brad-za/chastity/pictures/choc/v1/left-front.png

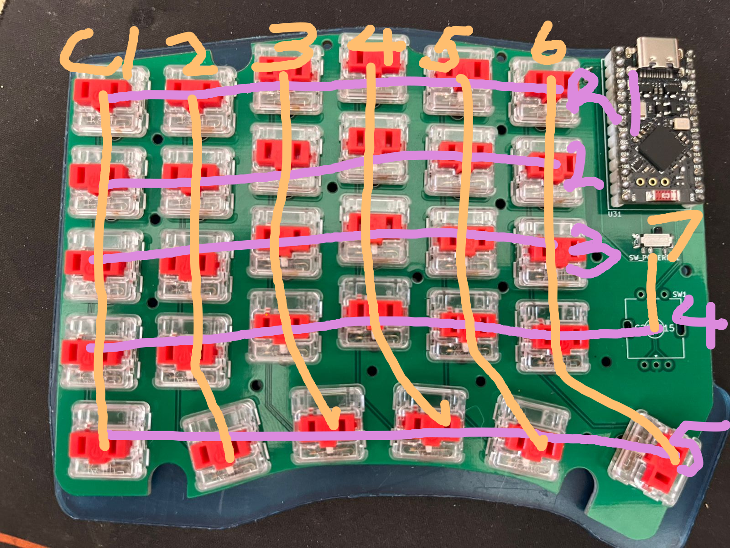
pictures/choc/v1/left-front.png
