brad-za/chastity/kicad/mx/V3/V3 - split/left/chastity.kicad_sch

## KiCad design kicad/mx/V3/V3 - split/left/chastity.kicad_sch (2025-07-24)

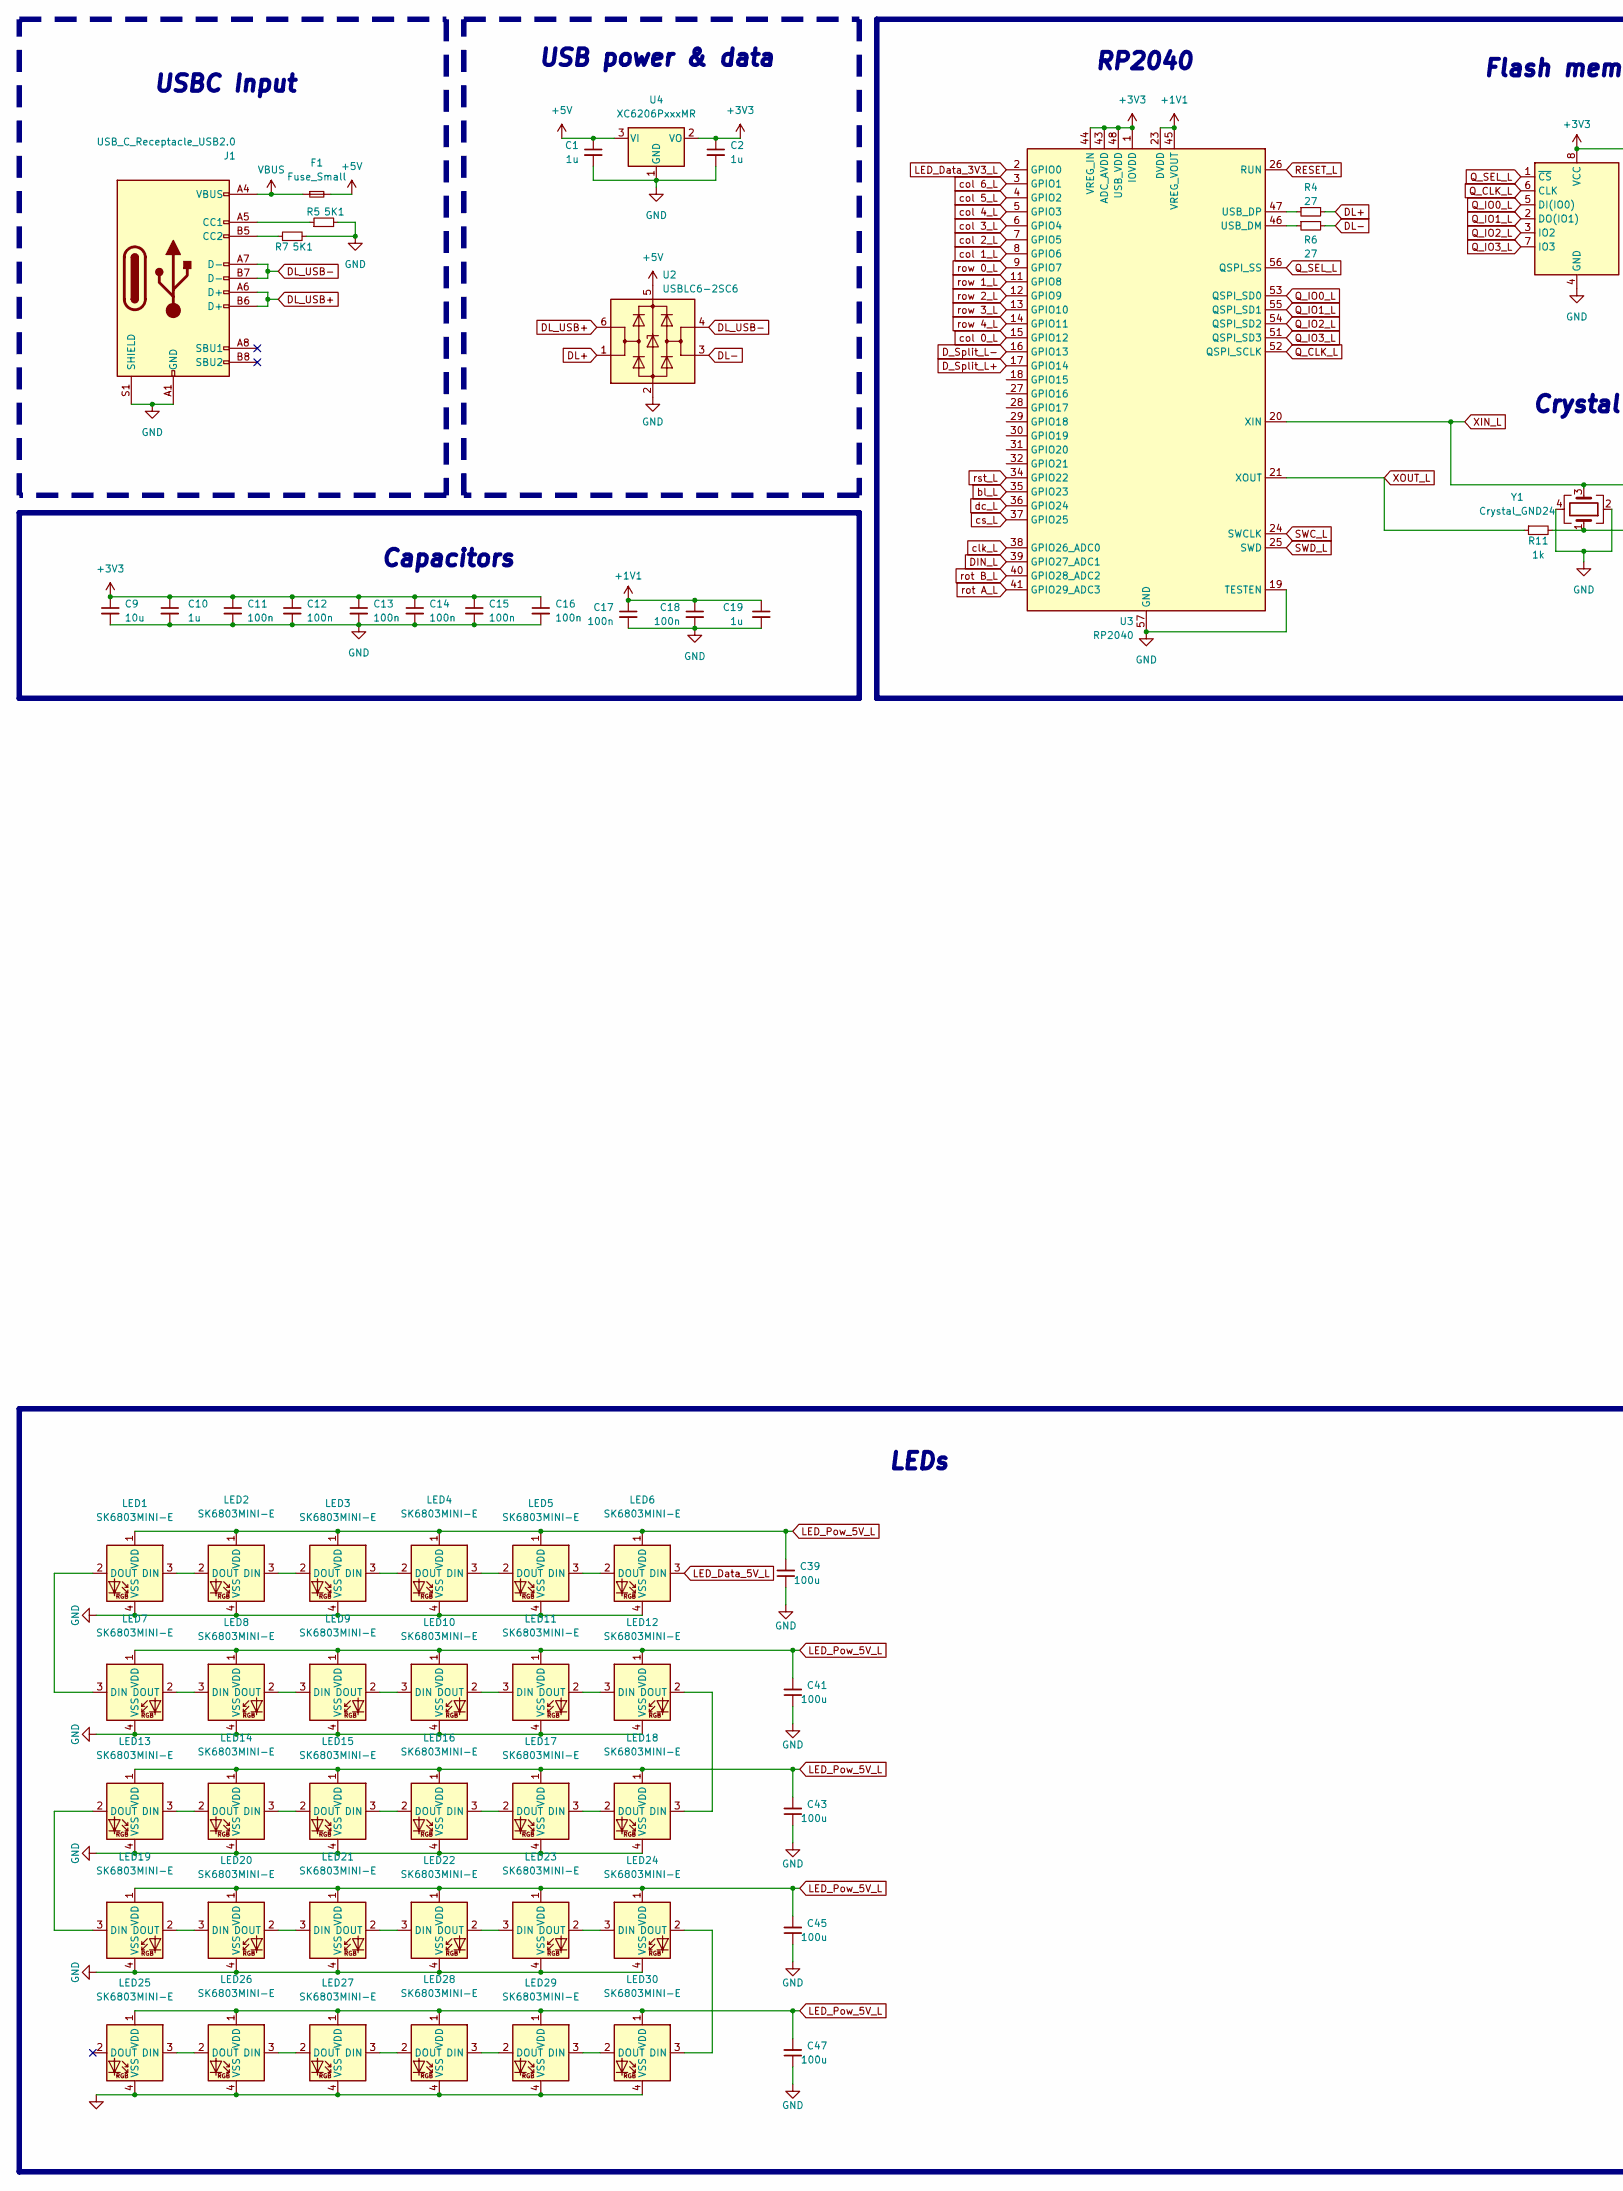
[picture p21: schematic chastity.kicad_sch, part in row 1, column 1]

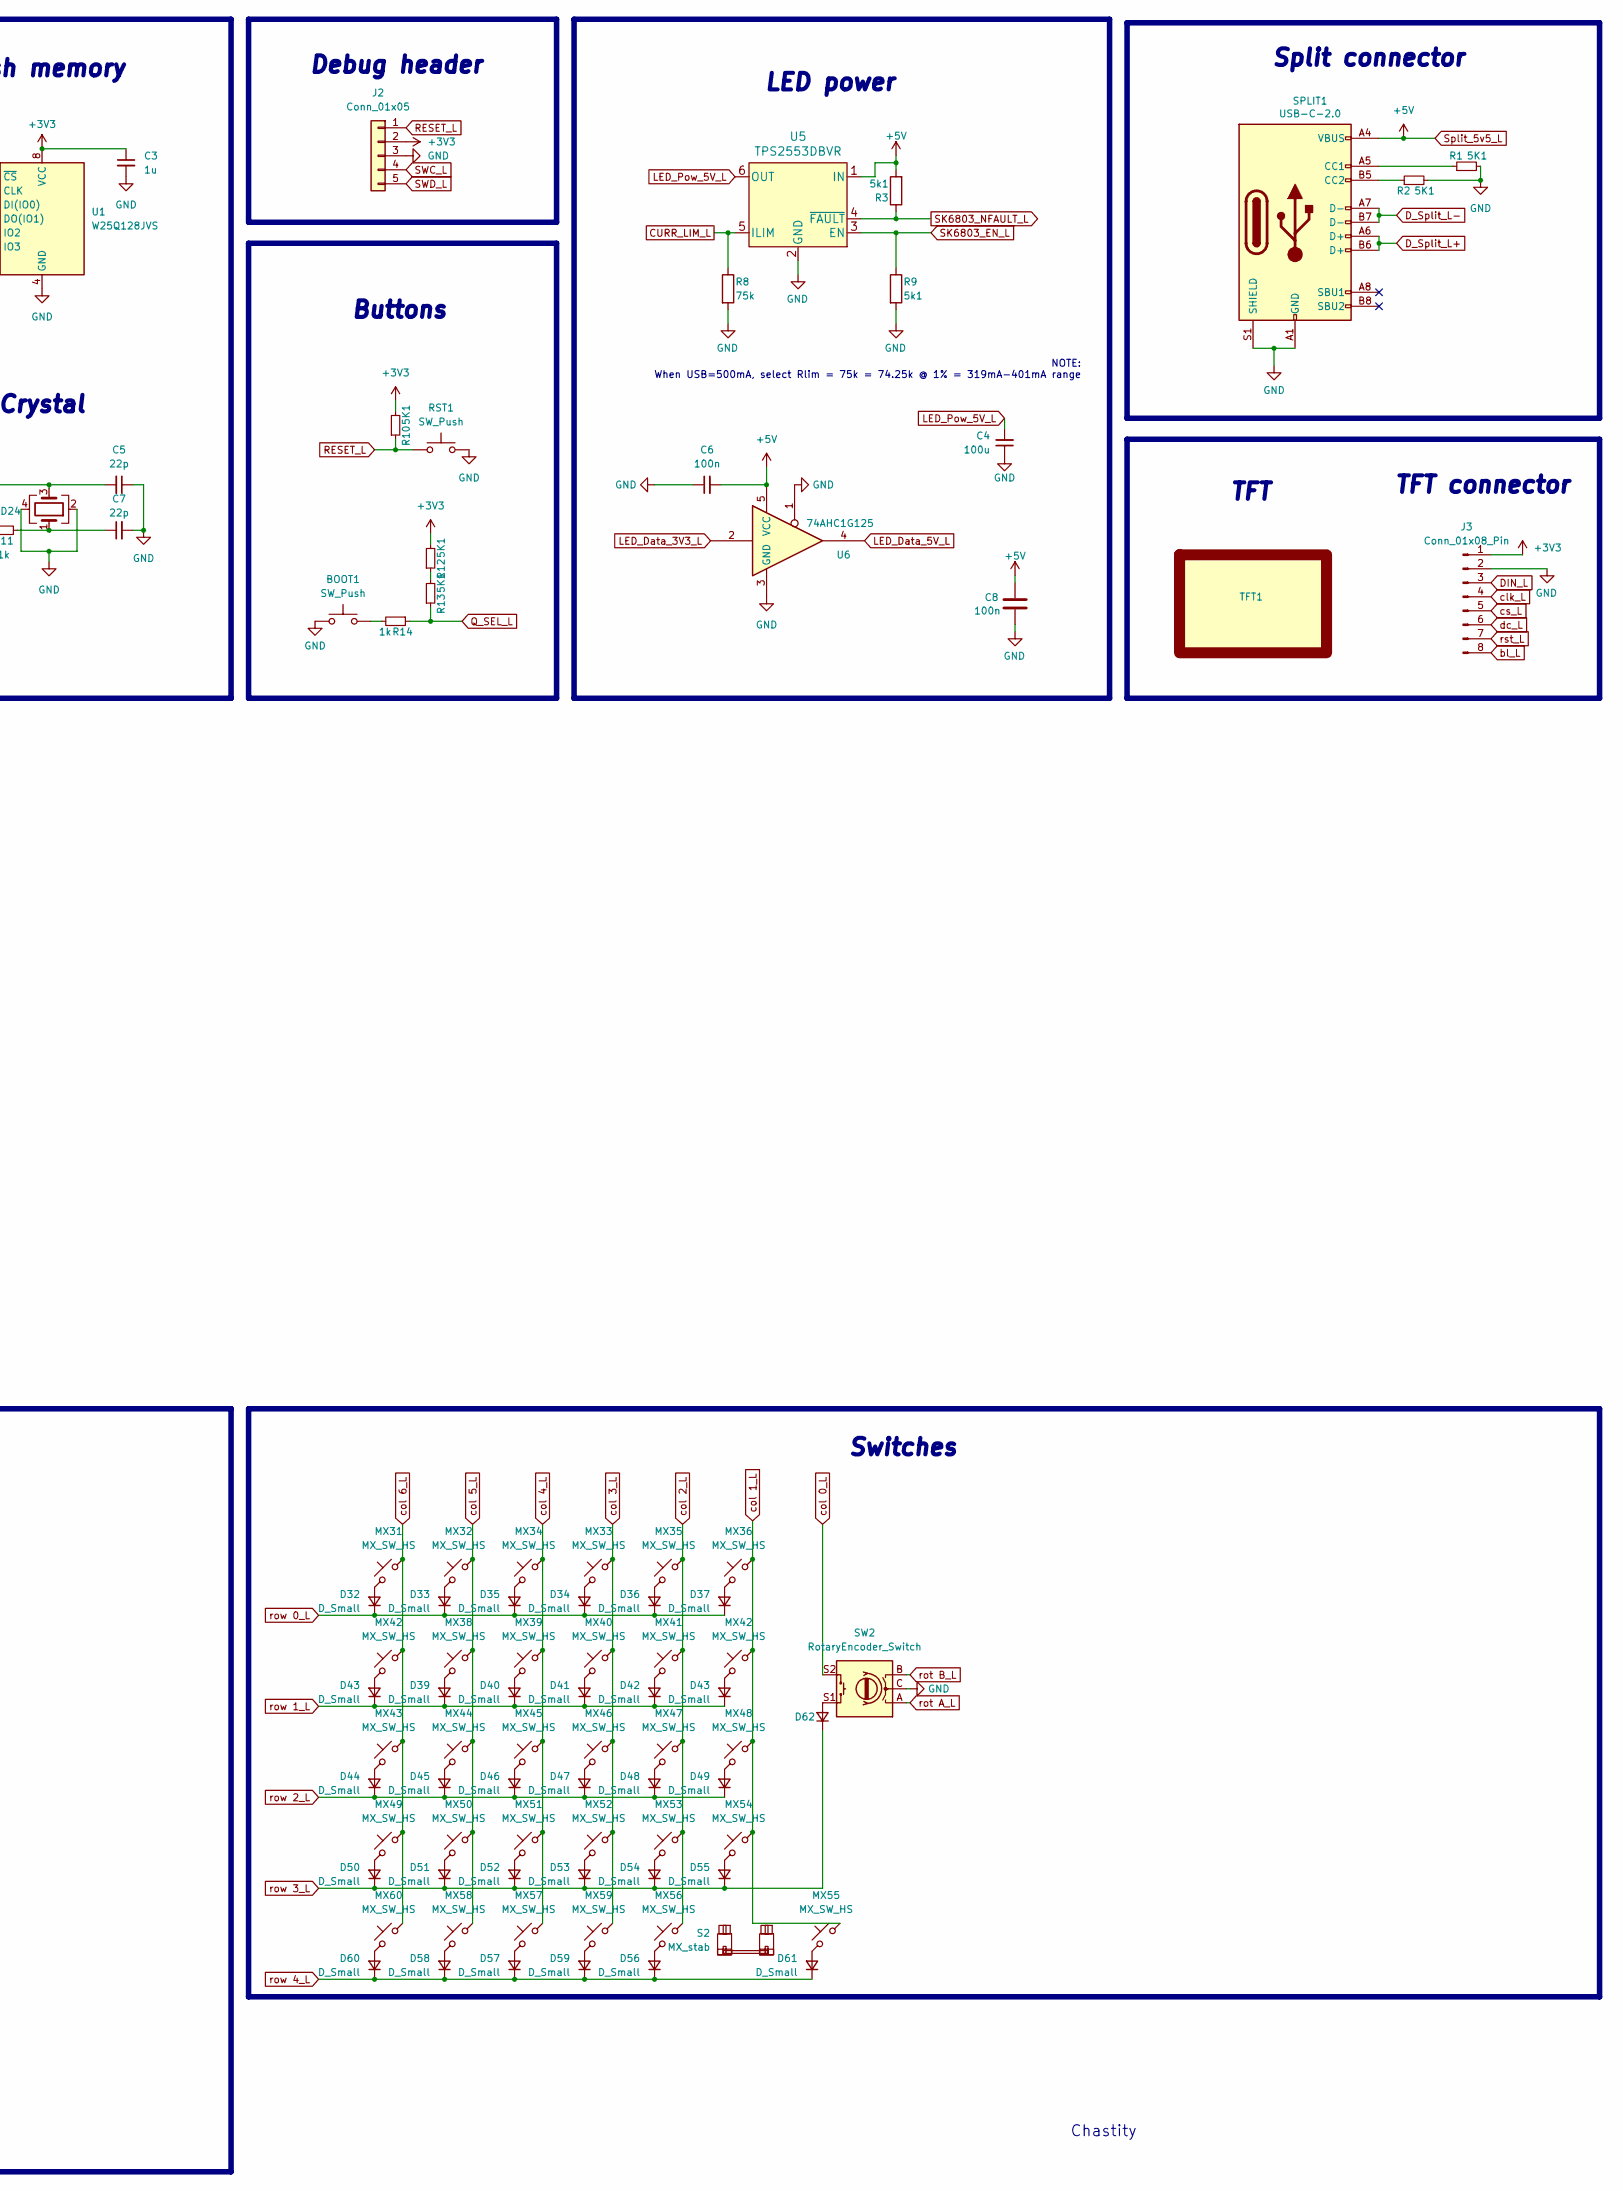
[picture p22: schematic chastity.kicad_sch, part in row 1, column 2]

Parts:
BOOT1: SW_Push; SW_SPST_TL3342
C1, C2, C3, C10, C19: 1u; C_0402_1005Metric
C4, C39, C41, C43, C45, C47: 100u; C_0402_1005Metric
C5, C7: 22p; C_0402_1005Metric
C6, C11, C12, C13, C14, C15, C16, C17, C18: 100n; C_0402_1005Metric
C8: 100n; C_0402_1005Metric; LCSC C1760
C9: 10u; C_0603_1608Metric
D32, D33, D34, D35, D36, D37, D39, D40, D41, D42, D43, D44, D45, D46, D47, D48, D49, D50, D51, D52, D53, D54, D55, D56, D57, D58, D59, D60, D61, D62: D_Small; D_SOD-123
F1: Fuse_Small; Fuse_1206_3216Metric
J1: USB_C_Receptacle_USB2.0; USB_C_Receptacle_HRO_TYPE-C-31-M-14
J2: Conn_01x05; PinSocket_1x05_P2.54mm_Horizontal
J3: Conn_01x08_Pin; PinHeader_1x08_P2.54mm_Horizontal
LED1, LED2, LED3, LED4, LED5, LED6, LED7, LED8, LED9, LED10, LED11, LED12, LED13, LED14, LED15, LED16, LED17, LED18, LED19, LED20, LED21, LED22, LED23, LED24, LED25, LED26, LED27, LED28, LED29, LED30: SK6803MINI-E; LED_MX_6028R
MX31, MX32, MX33, MX34, MX35, MX36, MX38, MX39, MX40, MX41, MX42, MX43, MX44, MX45, MX46, MX47, MX48, MX49, MX50, MX51, MX52, MX53, MX54, MX55, MX56, MX57, MX58, MX59, MX60: MX_SW_HS; SW_MX_HS_1u
R1, R2, R5, R7, R10, R12, R13: 5K1; R_0402_1005Metric
R3, R9: 5k1; R_0402_1005Metric; LCSC C27834
R4, R6: 27; R_0402_1005Metric
R8: 75k; R_0402_1005Metric; LCSC C17819
R11, R14: 1k; R_0402_1005Metric
RST1: SW_Push; SW_SPST_TL3342
S2: MX_stab; STAB_MX_P_2u
SPLIT1: USB-C-2.0; USB_C_Receptacle_HRO_TYPE-C-31-M-14
SW2: RotaryEncoder_Switch; ROT_Alps_EC11E-Switch
TFT1: TFT 1.47 waveshare
U1: W25Q128JVS; SOIC-8_5.23x5.23mm_P1.27mm
U2: USBLC6-2SC6; SOT-23-6
U3: RP2040; QFN-56-1EP_7x7mm_P0.4mm_EP3.2x3.2mm
U4: XC6206PxxxMR; SOT-23-3
U5: TPS2553DBVR; SOT-23-6; LCSC C55266
U6: 74AHC1G125; SOT-23-5
Y1: Crystal_GND24; Crystal_SMD_3225-4Pin_3.2x2.5mm

Connections:
+1V1: C17.1, C18.1, C19.1, U3.23 (DVDD), U3.45 (VREG_VOUT), U3.50 (DVDD)
+3V3: C2.1, C3.1, C9.1, C10.1, C11.1, C12.1, C13.1, C14.1, C15.1, C16.1, J2.2, J3.1, R10.2, R12.2, U1.8 (VCC), U3.1 (IOVDD), U3.10 (IOVDD), U3.22 (IOVDD), U3.33 (IOVDD), U3.42 (IOVDD), U3.43 (ADC_AVDD), U3.44 (VREG_IN), U3.48 (USB_VDD), U3.49 (IOVDD), U4.2 (VO)
+5V: C1.1, C6.2, C8.1, F1.2, R3.2, SPLIT1.A4 (VBUS), SPLIT1.A9 (VBUS), SPLIT1.B4 (VBUS), SPLIT1.B9 (VBUS), U2.5 (VBUS), U4.3 (VI), U5.1 (IN), U6.5 (VCC)
CURR_LIM_L: R8.1, U5.5 (ILIM)
DIN_L: J3.3, U3.39 (GPIO27_ADC1)
DL+: R4.2, U2.1 (I/O1)
DL-: R6.2, U2.3 (I/O2)
DL_USB+: J1.A6 (D+), J1.B6 (D+), U2.6 (I/O1)
DL_USB-: J1.A7 (D-), J1.B7 (D-), U2.4 (I/O2)
D_Split_L+: SPLIT1.A6 (D+), SPLIT1.B6 (D+), U3.17 (GPIO14)
D_Split_L-: SPLIT1.A7 (D-), SPLIT1.B7 (D-), U3.16 (GPIO13)
GND: BOOT1.1, C1.2, C2.2, C3.2, C4.1, C5.1, C6.1, C7.2, C8.2, C9.2, C10.2, C11.2, C12.2, C13.2, C14.2, C15.2, C16.2, C17.2, C18.2, C19.2, C39.1, C41.1, C43.1, C45.1, C47.1, J1.A1 (GND), J1.A12 (GND), J1.B1 (GND), J1.B12 (GND), J1.S1 (SHIELD), J2.3, J3.2, LED1.4 (VSS), LED2.4 (VSS), LED3.4 (VSS), LED4.4 (VSS), LED5.4 (VSS), LED6.4 (VSS), LED7.4 (VSS), LED8.4 (VSS), LED9.4 (VSS), LED10.4 (VSS), LED11.4 (VSS), LED12.4 (VSS), LED13.4 (VSS), LED14.4 (VSS), LED15.4 (VSS), LED16.4 (VSS), LED17.4 (VSS), LED18.4 (VSS), LED19.4 (VSS), LED20.4 (VSS), LED21.4 (VSS), LED22.4 (VSS), LED23.4 (VSS), LED24.4 (VSS), LED25.4 (VSS), LED26.4 (VSS), LED27.4 (VSS), LED28.4 (VSS), LED29.4 (VSS), LED30.4 (VSS), R1.2, R2.2, R5.2, R7.2, R8.2, R9.2, RST1.2, SPLIT1.A1 (GND), SPLIT1.A12 (GND), SPLIT1.B1 (GND), SPLIT1.B12 (GND), SPLIT1.S1 (SHIELD), SW2.C, U1.4 (GND), U2.2 (GND), U3.19 (TESTEN), U3.57 (GND), U4.1 (GND), U5.2 (GND), U6.1, U6.3 (GND), Y1.2, Y1.4
LED_Data_3V3_L: U3.2 (GPIO0), U6.2
LED_Data_5V_L: LED6.3 (DIN), U6.4
LED_Pow_5V_L: C4.2, C39.2, C41.2, C43.2, C45.2, C47.2, LED1.1 (VDD), LED2.1 (VDD), LED3.1 (VDD), LED4.1 (VDD), LED5.1 (VDD), LED6.1 (VDD), LED7.1 (VDD), LED8.1 (VDD), LED9.1 (VDD), LED10.1 (VDD), LED11.1 (VDD), LED12.1 (VDD), LED13.1 (VDD), LED14.1 (VDD), LED15.1 (VDD), LED16.1 (VDD), LED17.1 (VDD), LED18.1 (VDD), LED19.1 (VDD), LED20.1 (VDD), LED21.1 (VDD), LED22.1 (VDD), LED23.1 (VDD), LED24.1 (VDD), LED25.1 (VDD), LED26.1 (VDD), LED27.1 (VDD), LED28.1 (VDD), LED29.1 (VDD), LED30.1 (VDD), U5.6 (OUT)
unnamed: BOOT1.2, R14.2
unnamed: C7.1, R11.2, Y1.1
unnamed: D32.2 (A), MX31.2
unnamed: D33.2 (A), MX32.2
unnamed: D34.2 (A), MX33.2
unnamed: D35.2 (A), MX34.2
unnamed: D36.2 (A), MX35.2
unnamed: D37.2 (A), MX36.2
unnamed: D39.2 (A), MX38.2
unnamed: D40.2 (A), MX39.2
unnamed: D41.2 (A), MX40.2
unnamed: D42.2 (A), MX41.2
unnamed: D43.2 (A), MX42.2
unnamed: D44.2 (A), MX43.2
unnamed: D45.2 (A), MX44.2
unnamed: D46.2 (A), MX45.2
unnamed: D47.2 (A), MX46.2
unnamed: D48.2 (A), MX47.2
unnamed: D49.2 (A), MX48.2
unnamed: D50.2 (A), MX49.2
unnamed: D51.2 (A), MX50.2
unnamed: D52.2 (A), MX51.2
unnamed: D53.2 (A), MX52.2
unnamed: D54.2 (A), MX53.2
unnamed: D55.2 (A), MX54.2
unnamed: D56.2 (A), MX56.2
unnamed: D57.2 (A), MX57.2
unnamed: D58.2 (A), MX58.2
unnamed: D59.2 (A), MX59.2
unnamed: D60.2 (A), MX60.2
unnamed: D61.2 (A), MX55.2
unnamed: D62.2 (A), SW2.S1
unnamed: J1.A5 (CC1), R5.1
unnamed: J1.B5 (CC2), R7.1
unnamed: LED1.2 (DOUT), LED7.3 (DIN)
unnamed: LED1.3 (DIN), LED2.2 (DOUT)
unnamed: LED2.3 (DIN), LED3.2 (DOUT)
unnamed: LED3.3 (DIN), LED4.2 (DOUT)
unnamed: LED4.3 (DIN), LED5.2 (DOUT)
unnamed: LED5.3 (DIN), LED6.2 (DOUT)
unnamed: LED7.2 (DOUT), LED8.3 (DIN)
unnamed: LED8.2 (DOUT), LED9.3 (DIN)
unnamed: LED10.2 (DOUT), LED11.3 (DIN)
unnamed: LED9.2 (DOUT), LED10.3 (DIN)
unnamed: LED11.2 (DOUT), LED12.3 (DIN)
unnamed: LED12.2 (DOUT), LED18.3 (DIN)
unnamed: LED13.2 (DOUT), LED19.3 (DIN)
unnamed: LED13.3 (DIN), LED14.2 (DOUT)
unnamed: LED14.3 (DIN), LED15.2 (DOUT)
unnamed: LED15.3 (DIN), LED16.2 (DOUT)
unnamed: LED16.3 (DIN), LED17.2 (DOUT)
unnamed: LED17.3 (DIN), LED18.2 (DOUT)
unnamed: LED19.2 (DOUT), LED20.3 (DIN)
unnamed: LED20.2 (DOUT), LED21.3 (DIN)
unnamed: LED21.2 (DOUT), LED22.3 (DIN)
unnamed: LED22.2 (DOUT), LED23.3 (DIN)
unnamed: LED23.2 (DOUT), LED24.3 (DIN)
unnamed: LED24.2 (DOUT), LED30.3 (DIN)
unnamed: LED25.3 (DIN), LED26.2 (DOUT)
unnamed: LED26.3 (DIN), LED27.2 (DOUT)
unnamed: LED27.3 (DIN), LED28.2 (DOUT)
unnamed: LED28.3 (DIN), LED29.2 (DOUT)
unnamed: LED29.3 (DIN), LED30.2 (DOUT)
unnamed: R1.1, SPLIT1.A5 (CC1)
unnamed: R2.1, SPLIT1.B5 (CC2)
unnamed: R4.1, U3.47 (USB_DP)
unnamed: R6.1, U3.46 (USB_DM)
unnamed: R12.1, R13.2
Q_CLK_L: U1.6 (CLK), U3.52 (QSPI_SCLK)
Q_IO0_L: U1.5 (DI(IO0)), U3.53 (QSPI_SD0)
Q_IO1_L: U1.2 (DO(IO1)), U3.55 (QSPI_SD1)
Q_IO2_L: U1.3 (IO2), U3.54 (QSPI_SD2)
Q_IO3_L: U1.7 (IO3), U3.51 (QSPI_SD3)
Q_SEL_L: R13.1, R14.1, U1.1 (~CS), U3.56 (QSPI_SS)
RESET_L: J2.1, R10.1, RST1.1, U3.26 (RUN)
SK6803_EN_L: R9.1, U5.3 (EN)
SK6803_NFAULT_L: R3.1, U5.4 (~FAULT)
SWC_L: J2.4, U3.24 (SWCLK)
SWD_L: J2.5, U3.25 (SWD)
VBUS: F1.1, J1.A4 (VBUS), J1.A9 (VBUS), J1.B4 (VBUS), J1.B9 (VBUS)
XIN_L: C5.2, U3.20 (XIN), Y1.3
XOUT_L: R11.1, U3.21 (XOUT)
bl_L: J3.8, U3.35 (GPIO23)
clk_L: J3.4, U3.38 (GPIO26_ADC0)
col 0_L: SW2.S2, U3.15 (GPIO12)
col 1_L: MX36.1, MX42.1, MX48.1, MX54.1, MX55.1, U3.8 (GPIO6)
col 2_L: MX35.1, MX41.1, MX47.1, MX53.1, MX56.1, U3.7 (GPIO5)
col 3_L: MX33.1, MX40.1, MX46.1, MX52.1, MX59.1, U3.6 (GPIO4)
col 4_L: MX34.1, MX39.1, MX45.1, MX51.1, MX57.1, U3.5 (GPIO3)
col 5_L: MX32.1, MX38.1, MX44.1, MX50.1, MX58.1, U3.4 (GPIO2)
col 6_L: MX31.1, MX42.1, MX43.1, MX49.1, MX60.1, U3.3 (GPIO1)
cs_L: J3.5, U3.37 (GPIO25)
dc_L: J3.6, U3.36 (GPIO24)
rot A_L: SW2.A, U3.41 (GPIO29_ADC3)
rot B_L: SW2.B, U3.40 (GPIO28_ADC2)
row 0_L: D32.1 (K), D33.1 (K), D34.1 (K), D35.1 (K), D36.1 (K), D37.1 (K), U3.9 (GPIO7)
row 1_L: D39.1 (K), D40.1 (K), D41.1 (K), D42.1 (K), D43.1 (K), U3.11 (GPIO8)
row 2_L: D44.1 (K), D45.1 (K), D46.1 (K), D47.1 (K), D48.1 (K), D49.1 (K), U3.12 (GPIO9)
row 3_L: D50.1 (K), D51.1 (K), D52.1 (K), D53.1 (K), D54.1 (K), D55.1 (K), D62.1 (K), U3.13 (GPIO10)
row 4_L: D56.1 (K), D57.1 (K), D58.1 (K), D59.1 (K), D60.1 (K), D61.1 (K), U3.14 (GPIO11)
rst_L: J3.7, U3.34 (GPIO22)

Notes on the sheet:
LED power
Capacitors
Chastity
Buttons
NOTE: When USB=500mA, select Rlim = 75k = 74.25k @ 1% = 319mA-401mA range
USB power & data
Switches
TFT
Split connector
USBC Input
TFT connector
RP2040
Flash memory
Debug header
Crystal
LEDs
