brad-za/chastity/kicad/mx/V3/V3 - split/right/chastity.kicad_sch

## KiCad design kicad/mx/V3/V3 - split/right/chastity.kicad_sch (2025-07-24)

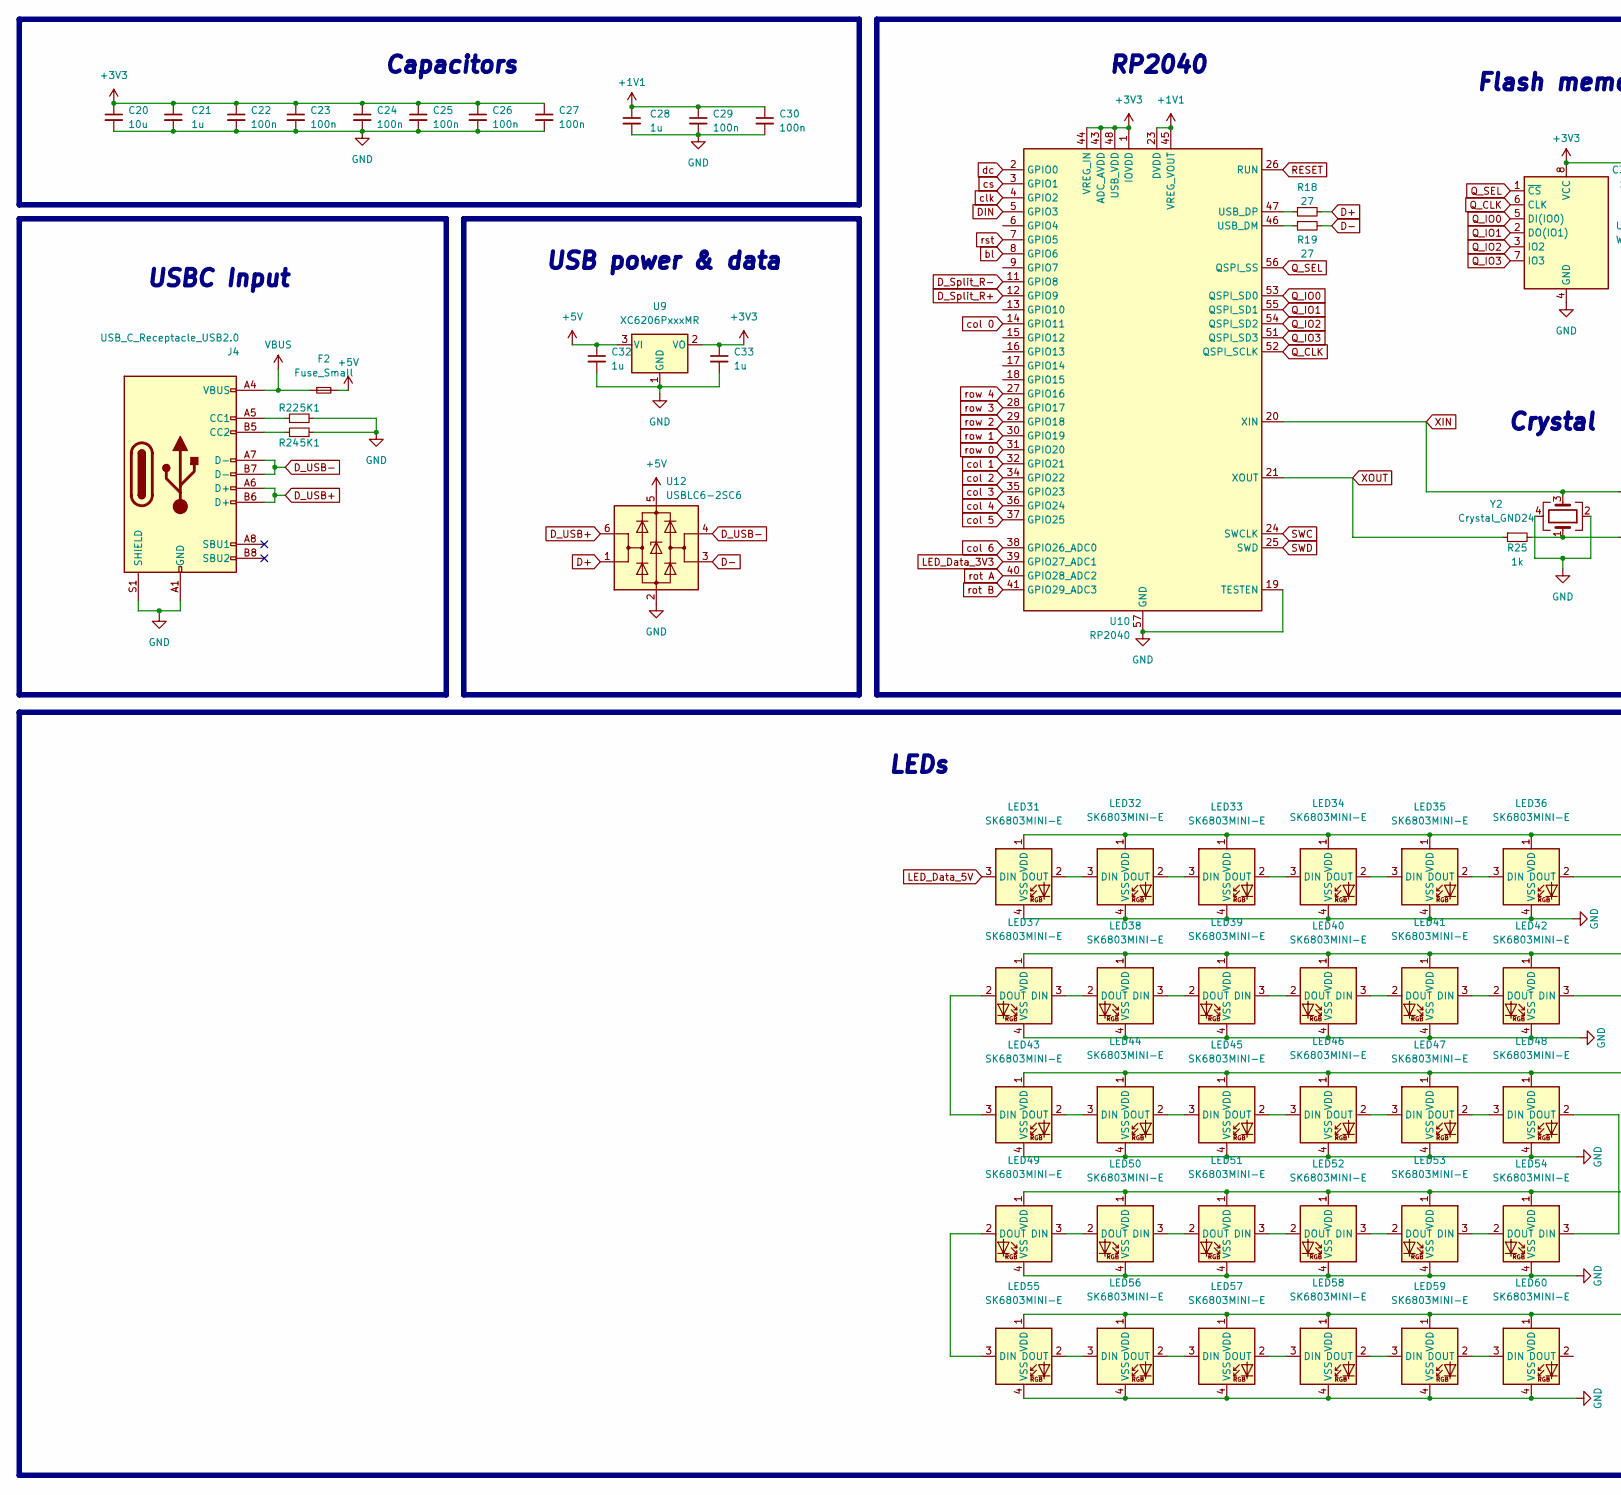
[picture p23: schematic chastity.kicad_sch, part in row 1, column 1]

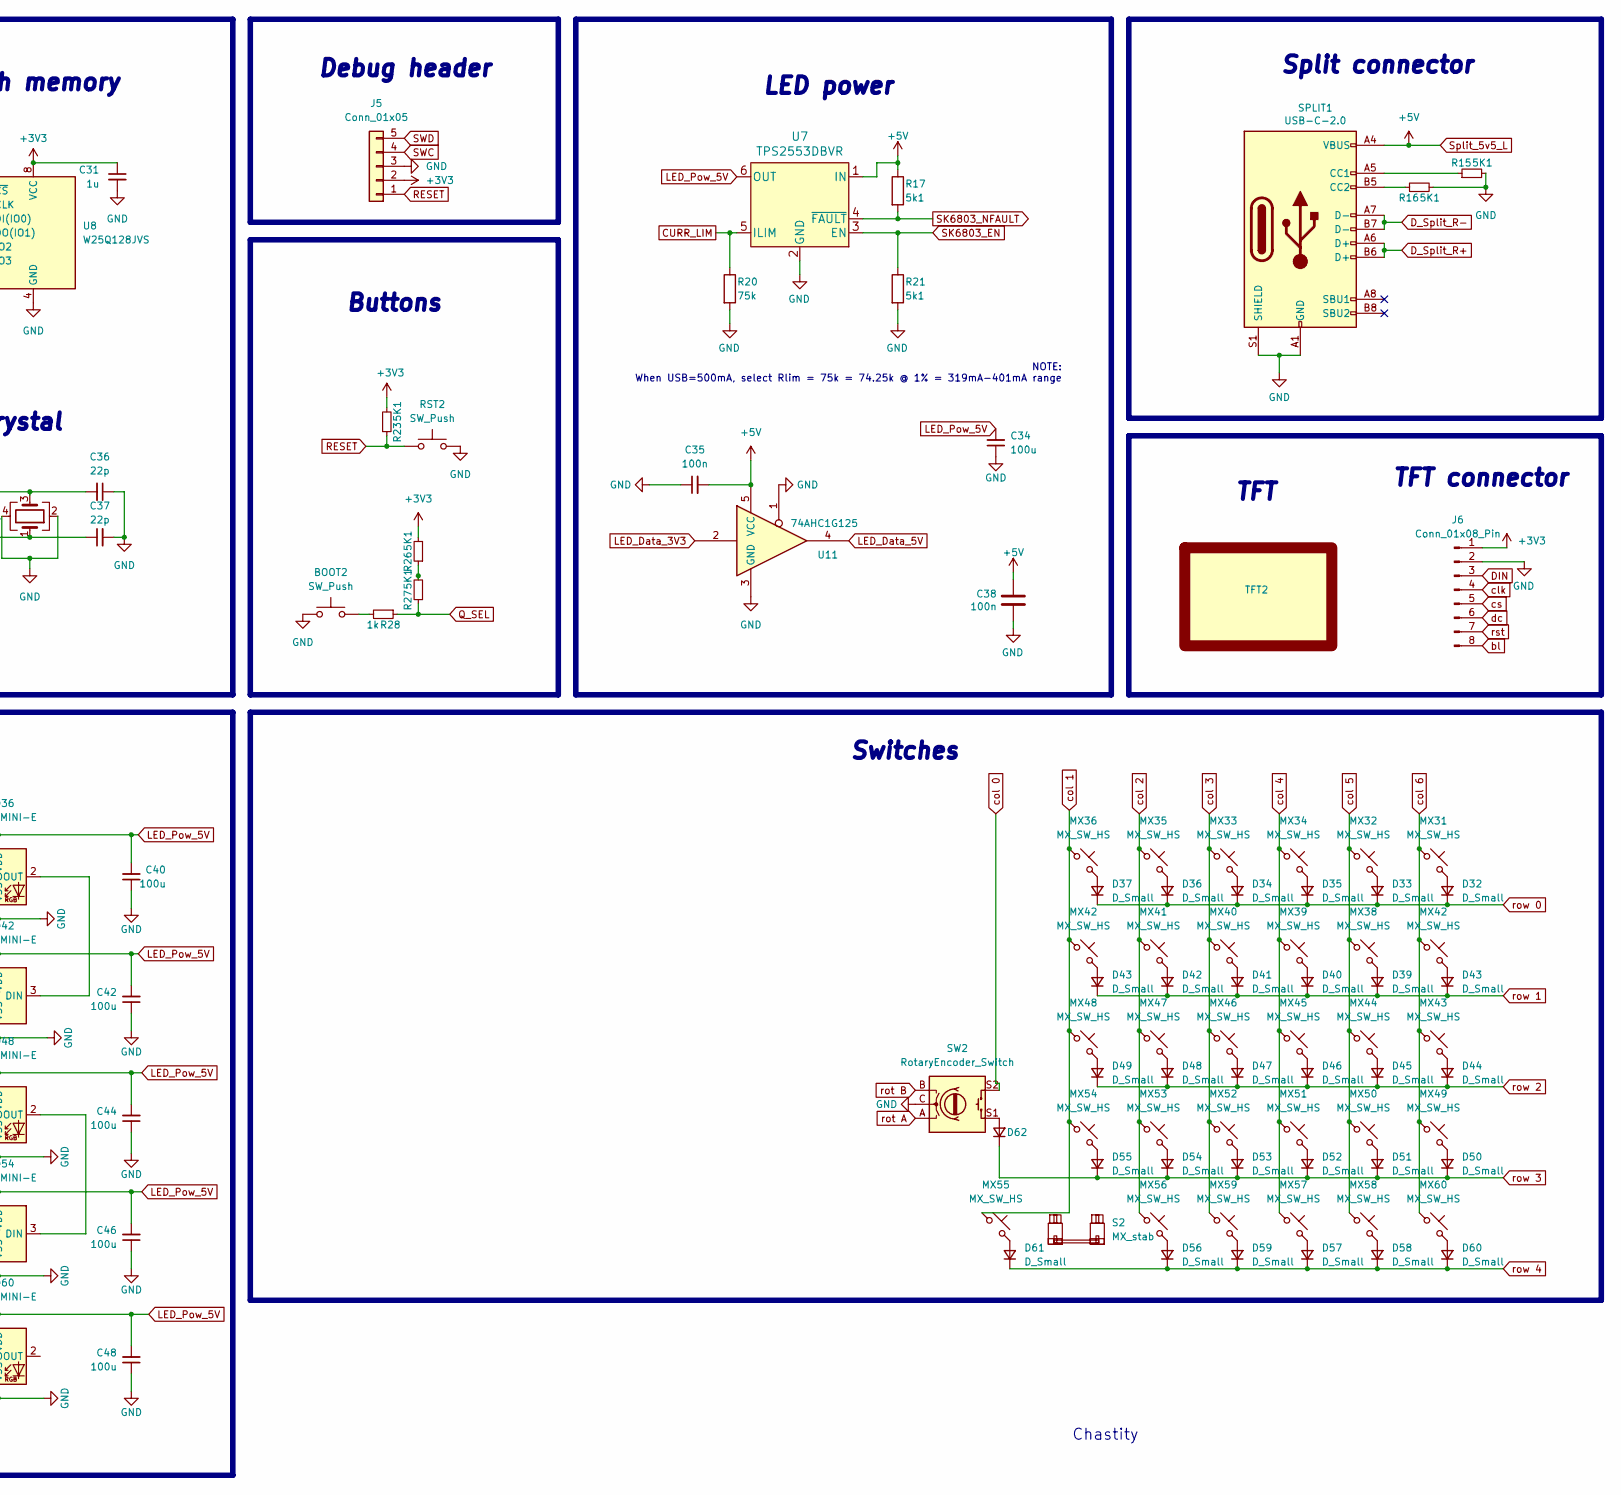
[picture p24: schematic chastity.kicad_sch, part in row 1, column 2]

Parts:
BOOT2: SW_Push; SW_SPST_TL3342
C20: 10u; C_0603_1608Metric
C21, C28, C31, C32, C33: 1u; C_0402_1005Metric
C22, C23, C24, C25, C26, C27, C29, C30, C35: 100n; C_0402_1005Metric
C34, C40, C42, C44, C46, C48: 100u; C_0402_1005Metric
C36, C37: 22p; C_0402_1005Metric
C38: 100n; C_0402_1005Metric; LCSC C1760
D32, D33, D34, D35, D36, D37, D39, D40, D41, D42, D43, D44, D45, D46, D47, D48, D49, D50, D51, D52, D53, D54, D55, D56, D57, D58, D59, D60, D61, D62: D_Small; D_SOD-123
F2: Fuse_Small; Fuse_1206_3216Metric
J4: USB_C_Receptacle_USB2.0; USB_C_Receptacle_HRO_TYPE-C-31-M-14
J5: Conn_01x05; PinSocket_1x05_P2.54mm_Horizontal
J6: Conn_01x08_Pin; PinHeader_1x08_P2.54mm_Horizontal
LED31, LED32, LED33, LED34, LED35, LED36, LED37, LED38, LED39, LED40, LED41, LED42, LED43, LED44, LED45, LED46, LED47, LED48, LED49, LED50, LED51, LED52, LED53, LED54, LED55, LED56, LED57, LED58, LED59, LED60: SK6803MINI-E; LED_MX_6028R
MX31, MX32, MX33, MX34, MX35, MX36, MX38, MX39, MX40, MX41, MX42, MX43, MX44, MX45, MX46, MX47, MX48, MX49, MX50, MX51, MX52, MX53, MX54, MX55, MX56, MX57, MX58, MX59, MX60: MX_SW_HS; SW_MX_HS_1u
R15, R16, R22, R23, R24, R26, R27: 5K1; R_0402_1005Metric
R17, R21: 5k1; C_0402_1005Metric; LCSC C27834
R18, R19: 27; R_0402_1005Metric
R20: 75k; C_0402_1005Metric; LCSC C17819
R25, R28: 1k; R_0402_1005Metric
RST2: SW_Push; SW_SPST_TL3342
S2: MX_stab; STAB_MX_P_2u
SPLIT1: USB-C-2.0; USB_C_Receptacle_HRO_TYPE-C-31-M-14
SW2: RotaryEncoder_Switch; ROT_Alps_EC11E-Switch
TFT2: TFT 1.47 waveshare
U7: TPS2553DBVR; SOT-23-6; LCSC C55266
U8: W25Q128JVS; SOIC-8_5.23x5.23mm_P1.27mm
U9: XC6206PxxxMR; SOT-23-3
U10: RP2040; QFN-56-1EP_7x7mm_P0.4mm_EP3.2x3.2mm
U11: 74AHC1G125; SOT-23-5
U12: USBLC6-2SC6; SOT-23-6
Y2: Crystal_GND24; Crystal_SMD_3225-4Pin_3.2x2.5mm

Connections:
+1V1: C28.1, C29.1, C30.1, U10.23 (DVDD), U10.45 (VREG_VOUT), U10.50 (DVDD)
+3V3: C20.1, C21.1, C22.1, C23.1, C24.1, C25.1, C26.1, C27.1, C31.1, C33.1, J5.2, J6.1, R23.2, R26.2, U8.8 (VCC), U9.2 (VO), U10.1 (IOVDD), U10.10 (IOVDD), U10.22 (IOVDD), U10.33 (IOVDD), U10.42 (IOVDD), U10.43 (ADC_AVDD), U10.44 (VREG_IN), U10.48 (USB_VDD), U10.49 (IOVDD)
+5V: C32.1, C35.2, C38.1, F2.2, R17.1, SPLIT1.A4 (VBUS), SPLIT1.A9 (VBUS), SPLIT1.B4 (VBUS), SPLIT1.B9 (VBUS), U7.1 (IN), U9.3 (VI), U11.5 (VCC), U12.5 (VBUS)
CURR_LIM: R20.1, U7.5 (ILIM)
D+: R18.2, U12.1 (I/O1)
D-: R19.2, U12.3 (I/O2)
DIN: J6.3, U10.5 (GPIO3)
D_Split_R+: SPLIT1.A6 (D+), SPLIT1.B6 (D+), U10.12 (GPIO9)
D_Split_R-: SPLIT1.A7 (D-), SPLIT1.B7 (D-), U10.11 (GPIO8)
D_USB+: J4.A6 (D+), J4.B6 (D+), U12.6 (I/O1)
D_USB-: J4.A7 (D-), J4.B7 (D-), U12.4 (I/O2)
GND: BOOT2.1, C20.2, C21.2, C22.2, C23.2, C24.2, C25.2, C26.2, C27.2, C28.2, C29.2, C30.2, C31.2, C32.2, C33.2, C34.1, C35.1, C36.1, C37.2, C38.2, C40.1, C42.1, C44.1, C46.1, C48.1, J4.A1 (GND), J4.A12 (GND), J4.B1 (GND), J4.B12 (GND), J4.S1 (SHIELD), J5.3, J6.2, LED31.4 (VSS), LED32.4 (VSS), LED33.4 (VSS), LED34.4 (VSS), LED35.4 (VSS), LED36.4 (VSS), LED37.4 (VSS), LED38.4 (VSS), LED39.4 (VSS), LED40.4 (VSS), LED41.4 (VSS), LED42.4 (VSS), LED43.4 (VSS), LED44.4 (VSS), LED45.4 (VSS), LED46.4 (VSS), LED47.4 (VSS), LED48.4 (VSS), LED49.4 (VSS), LED50.4 (VSS), LED51.4 (VSS), LED52.4 (VSS), LED53.4 (VSS), LED54.4 (VSS), LED55.4 (VSS), LED56.4 (VSS), LED57.4 (VSS), LED58.4 (VSS), LED59.4 (VSS), LED60.4 (VSS), R15.2, R16.2, R20.2, R21.2, R22.2, R24.2, RST2.1, SPLIT1.A1 (GND), SPLIT1.A12 (GND), SPLIT1.B1 (GND), SPLIT1.B12 (GND), SPLIT1.S1 (SHIELD), SW2.C, U7.2 (GND), U8.4 (GND), U9.1 (GND), U10.19 (TESTEN), U10.57 (GND), U11.1, U11.3 (GND), U12.2 (GND), Y2.2, Y2.4
LED_Data_3V3: U10.39 (GPIO27_ADC1), U11.2
LED_Data_5V: LED31.3 (DIN), U11.4
LED_Pow_5V: C34.2, C40.2, C42.2, C44.2, C46.2, C48.2, LED31.1 (VDD), LED32.1 (VDD), LED33.1 (VDD), LED34.1 (VDD), LED35.1 (VDD), LED36.1 (VDD), LED37.1 (VDD), LED38.1 (VDD), LED39.1 (VDD), LED40.1 (VDD), LED41.1 (VDD), LED42.1 (VDD), LED43.1 (VDD), LED44.1 (VDD), LED45.1 (VDD), LED46.1 (VDD), LED47.1 (VDD), LED48.1 (VDD), LED49.1 (VDD), LED50.1 (VDD), LED51.1 (VDD), LED52.1 (VDD), LED53.1 (VDD), LED54.1 (VDD), LED55.1 (VDD), LED56.1 (VDD), LED57.1 (VDD), LED58.1 (VDD), LED59.1 (VDD), LED60.1 (VDD), U7.6 (OUT)
unnamed: BOOT2.2, R28.2
unnamed: C37.1, R25.2, Y2.1
unnamed: D32.2 (A), MX31.2
unnamed: D33.2 (A), MX32.2
unnamed: D34.2 (A), MX33.2
unnamed: D35.2 (A), MX34.2
unnamed: D36.2 (A), MX35.2
unnamed: D37.2 (A), MX36.2
unnamed: D39.2 (A), MX38.2
unnamed: D40.2 (A), MX39.2
unnamed: D41.2 (A), MX40.2
unnamed: D42.2 (A), MX41.2
unnamed: D43.2 (A), MX42.2
unnamed: D44.2 (A), MX43.2
unnamed: D45.2 (A), MX44.2
unnamed: D46.2 (A), MX45.2
unnamed: D47.2 (A), MX46.2
unnamed: D48.2 (A), MX47.2
unnamed: D49.2 (A), MX48.2
unnamed: D50.2 (A), MX49.2
unnamed: D51.2 (A), MX50.2
unnamed: D52.2 (A), MX51.2
unnamed: D53.2 (A), MX52.2
unnamed: D54.2 (A), MX53.2
unnamed: D55.2 (A), MX54.2
unnamed: D56.2 (A), MX56.2
unnamed: D57.2 (A), MX57.2
unnamed: D58.2 (A), MX58.2
unnamed: D59.2 (A), MX59.2
unnamed: D60.2 (A), MX60.2
unnamed: D61.2 (A), MX55.2
unnamed: D62.2 (A), SW2.S1
unnamed: J4.A5 (CC1), R22.1
unnamed: J4.B5 (CC2), R24.1
unnamed: LED31.2 (DOUT), LED32.3 (DIN)
unnamed: LED32.2 (DOUT), LED33.3 (DIN)
unnamed: LED33.2 (DOUT), LED34.3 (DIN)
unnamed: LED34.2 (DOUT), LED35.3 (DIN)
unnamed: LED35.2 (DOUT), LED36.3 (DIN)
unnamed: LED36.2 (DOUT), LED42.3 (DIN)
unnamed: LED37.2 (DOUT), LED43.3 (DIN)
unnamed: LED37.3 (DIN), LED38.2 (DOUT)
unnamed: LED38.3 (DIN), LED39.2 (DOUT)
unnamed: LED39.3 (DIN), LED40.2 (DOUT)
unnamed: LED40.3 (DIN), LED41.2 (DOUT)
unnamed: LED41.3 (DIN), LED42.2 (DOUT)
unnamed: LED43.2 (DOUT), LED44.3 (DIN)
unnamed: LED44.2 (DOUT), LED45.3 (DIN)
unnamed: LED45.2 (DOUT), LED46.3 (DIN)
unnamed: LED46.2 (DOUT), LED47.3 (DIN)
unnamed: LED47.2 (DOUT), LED48.3 (DIN)
unnamed: LED48.2 (DOUT), LED54.3 (DIN)
unnamed: LED49.2 (DOUT), LED55.3 (DIN)
unnamed: LED49.3 (DIN), LED50.2 (DOUT)
unnamed: LED50.3 (DIN), LED51.2 (DOUT)
unnamed: LED51.3 (DIN), LED52.2 (DOUT)
unnamed: LED52.3 (DIN), LED53.2 (DOUT)
unnamed: LED53.3 (DIN), LED54.2 (DOUT)
unnamed: LED55.2 (DOUT), LED56.3 (DIN)
unnamed: LED56.2 (DOUT), LED57.3 (DIN)
unnamed: LED57.2 (DOUT), LED58.3 (DIN)
unnamed: LED58.2 (DOUT), LED59.3 (DIN)
unnamed: LED59.2 (DOUT), LED60.3 (DIN)
unnamed: R15.1, SPLIT1.A5 (CC1)
unnamed: R16.1, SPLIT1.B5 (CC2)
unnamed: R18.1, U10.47 (USB_DP)
unnamed: R19.1, U10.46 (USB_DM)
unnamed: R26.1, R27.2
Q_CLK: U8.6 (CLK), U10.52 (QSPI_SCLK)
Q_IO0: U8.5 (DI(IO0)), U10.53 (QSPI_SD0)
Q_IO1: U8.2 (DO(IO1)), U10.55 (QSPI_SD1)
Q_IO2: U8.3 (IO2), U10.54 (QSPI_SD2)
Q_IO3: U8.7 (IO3), U10.51 (QSPI_SD3)
Q_SEL: R27.1, R28.1, U8.1 (~CS), U10.56 (QSPI_SS)
RESET: J5.1, R23.1, RST2.2, U10.26 (RUN)
SK6803_EN: R21.1, U7.3 (EN)
SK6803_NFAULT: R17.2, U7.4 (~FAULT)
SWC: J5.4, U10.24 (SWCLK)
SWD: J5.5, U10.25 (SWD)
VBUS: F2.1, J4.A4 (VBUS), J4.A9 (VBUS), J4.B4 (VBUS), J4.B9 (VBUS)
XIN: C36.2, U10.20 (XIN), Y2.3
XOUT: R25.1, U10.21 (XOUT)
bl: J6.8, U10.8 (GPIO6)
clk: J6.4, U10.4 (GPIO2)
col 0: SW2.S2, U10.14 (GPIO11)
col 1: MX36.1, MX42.1, MX48.1, MX54.1, MX55.1, U10.32 (GPIO21)
col 2: MX35.1, MX41.1, MX47.1, MX53.1, MX56.1, U10.34 (GPIO22)
col 3: MX33.1, MX40.1, MX46.1, MX52.1, MX59.1, U10.35 (GPIO23)
col 4: MX34.1, MX39.1, MX45.1, MX51.1, MX57.1, U10.36 (GPIO24)
col 5: MX32.1, MX38.1, MX44.1, MX50.1, MX58.1, U10.37 (GPIO25)
col 6: MX31.1, MX42.1, MX43.1, MX49.1, MX60.1, U10.38 (GPIO26_ADC0)
cs: J6.5, U10.3 (GPIO1)
dc: J6.6, U10.2 (GPIO0)
rot A: SW2.A, U10.40 (GPIO28_ADC2)
rot B: SW2.B, U10.41 (GPIO29_ADC3)
row 0: D32.1 (K), D33.1 (K), D34.1 (K), D35.1 (K), D36.1 (K), D37.1 (K), U10.31 (GPIO20)
row 1: D39.1 (K), D40.1 (K), D41.1 (K), D42.1 (K), D43.1 (K), U10.30 (GPIO19)
row 2: D44.1 (K), D45.1 (K), D46.1 (K), D47.1 (K), D48.1 (K), D49.1 (K), U10.29 (GPIO18)
row 3: D50.1 (K), D51.1 (K), D52.1 (K), D53.1 (K), D54.1 (K), D55.1 (K), D62.1 (K), U10.28 (GPIO17)
row 4: D56.1 (K), D57.1 (K), D58.1 (K), D59.1 (K), D60.1 (K), D61.1 (K), U10.27 (GPIO16)
rst: J6.7, U10.7 (GPIO5)

Notes on the sheet:
LED power
Chastity
TFT connector
NOTE: When USB=500mA, select Rlim = 75k = 74.25k @ 1% = 319mA-401mA range
Flash memory
Switches
Crystal
TFT
Buttons
USB power & data
Split connector
USBC Input
Capacitors
RP2040
LEDs
Debug header
